Smashcat/tetris-business-card/firmware/tetris-business-card/tetris-business-card/maze.c

/*
 * maze.c
 *
 * Created: 03/10/2021 18:47:32
 *  Author: Scott Porter
 */ 

#include "funcs.h"
#include "maze.h"

uint8_t maze[4 * 32];	// 32 x 32 pixel maze

void playMaze(void){
	 // This is left as an exercise for the reader :-)
}
